ETG153/bluetooth-speaker/Hardware/Tweeter Amplifier/PAM8403 Amplifier Board R2 PCB.pdf

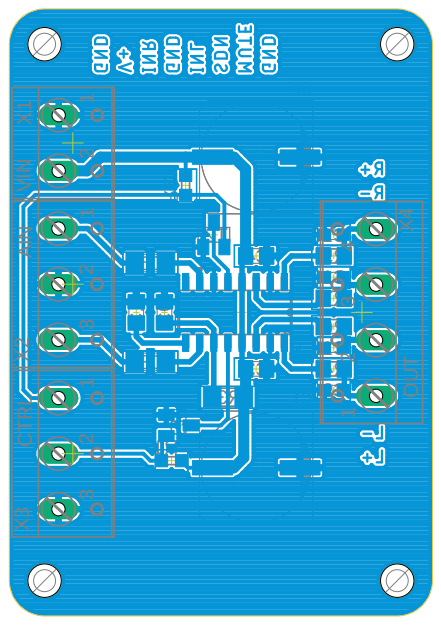
[picture p20: page 1]
