ETG153/bluetooth-speaker/Hardware/Tweeter Amplifier/PAM8403 Amplifier Board R2 SCH.pdf

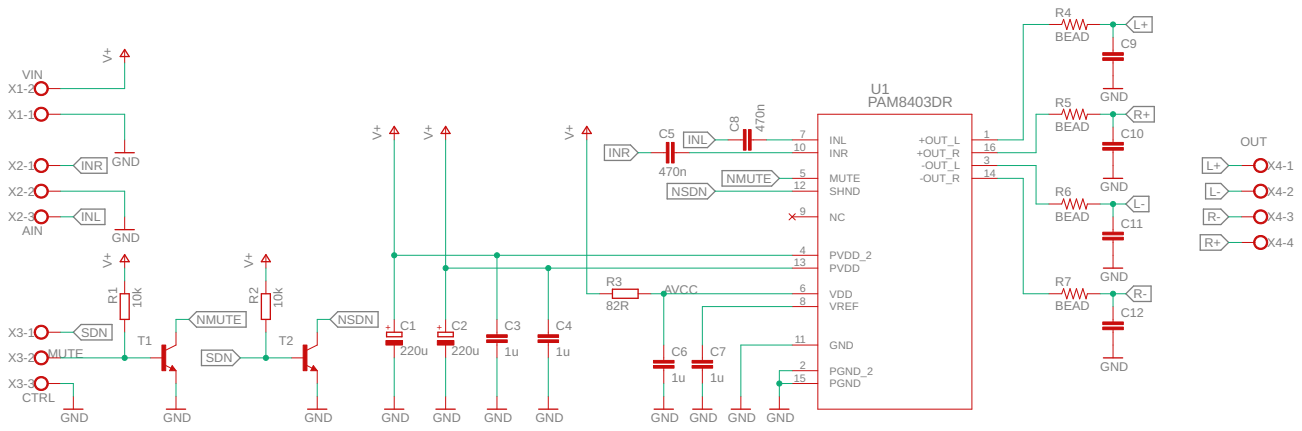
[picture p21: page 1]
